jerryok826/Battery-PWR-Board/Pictures/IMG_7567.jpeg

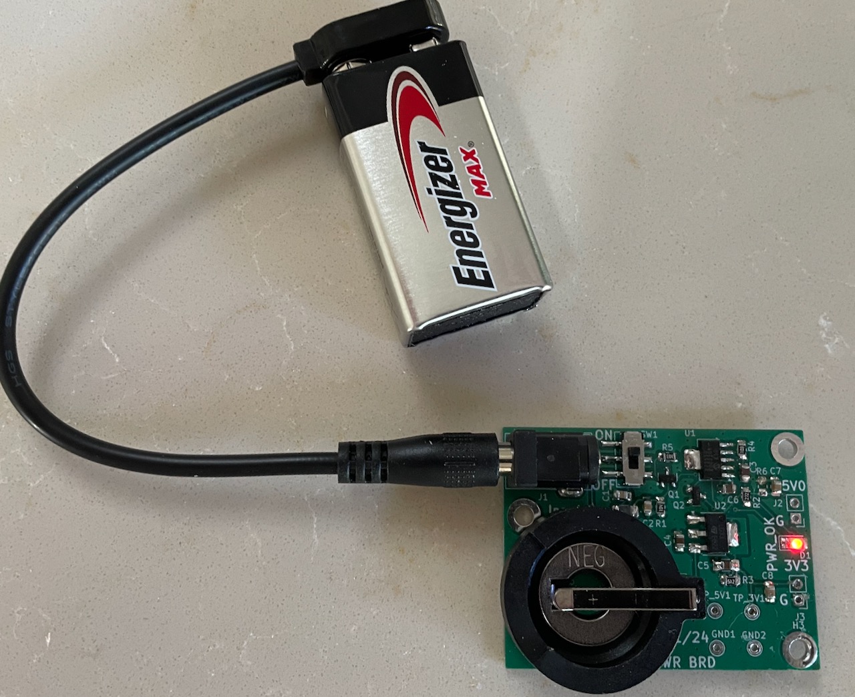
Pictures/IMG_7567.jpeg
